joeycastillo/Sensor-Watch/PCB/Sensor Boards/Eagle (Legacy Boards)/Untested - WIP - Not Recommended/OSO-MISC-21-015 Temperature and Light Board.brd

## EAGLE design PCB/Sensor Boards/Eagle (Legacy Boards)/Untested - WIP - Not Recommended/OSO-MISC-21-015 Temperature and Light Board.brd (2021-10-25, an earlier design)

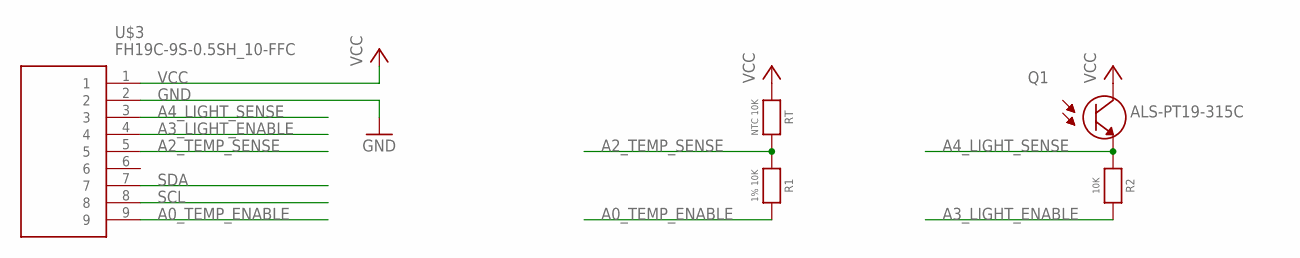
[picture p31: schematic OSO-MISC-21-015 Temperature and Light Board.sch]

Parts:
Q1: ALS-PT19-315C; XDCR_ALS-PT19-315C/L177/TR8_REVERSE
R1: 1% 10K; _0603MP
R2: 10K; _0603MP
RT: NTC 10K; _0603
U$3: FH19C-9S-0.5SH_10-FFC; FH19C9S05SH10-FFC

Connections:
A0_TEMP_ENABLE: R1.2, U$3.9
A2_TEMP_SENSE: R1.1, RT.2, U$3.5
A3_LIGHT_ENABLE: R2.2, U$3.4
A4_LIGHT_SENSE: Q1.2 (E), R2.1, U$3.3
GND: U$3.2
SCL: U$3.8
SDA: U$3.7
VCC: Q1.1 (C), RT.1, U$3.1

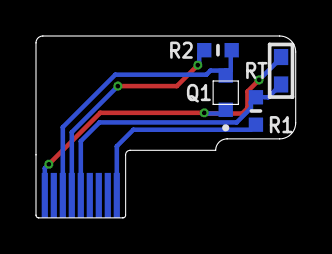
[picture p32: board OSO-MISC-21-015 Temperature and Light Board.brd from below]

Board: 2 copper layers, 14.4 x 10.1 mm, 5 parts (4 on the bottom side), 5 nets.
