joeycastillo/Sensor-Watch/PCB/Sensor Boards/Eagle (Legacy Boards)/Tested/OSO-MISC-21-021 Sensor Watch Motion II.brd

## EAGLE design PCB/Sensor Boards/Eagle (Legacy Boards)/Tested/OSO-MISC-21-021 Sensor Watch Motion II.brd (2022-02-05, an earlier design)

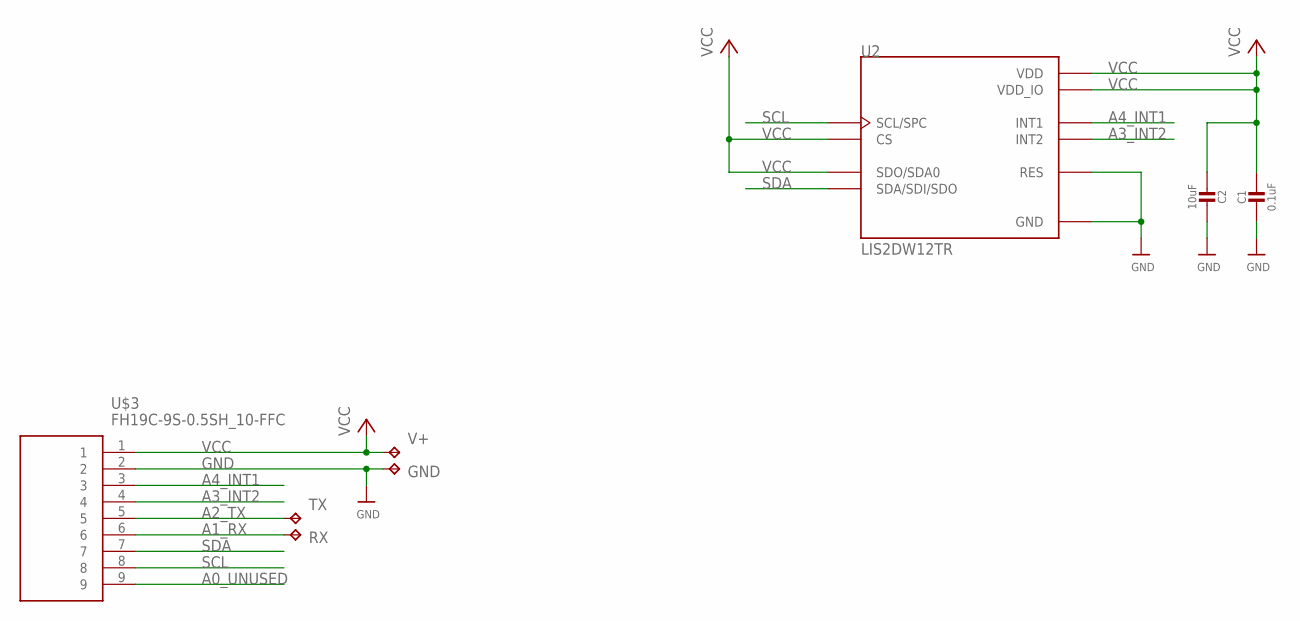
[picture p33: schematic OSO-MISC-21-021 Sensor Watch Motion II.sch]

Parts:
C1: 0.1uF; _0603MP
C2: 10uF; _0603MP
GND: TPB1,27; B1,27
RX: TPB1,27; B1,27
TX: TPB1,27; B1,27
U2: LIS2DW12TR; LGA12R50P4X4_200X200X70
U$3: FH19C-9S-0.5SH_10-FFC; FH19C9S05SH10-FFC
V+: TPB1,27; B1,27

Connections:
A0_UNUSED: U$3.9
A1_RX: RX.TP, U$3.6
A2_TX: TX.TP, U$3.5
A3_INT2: U2.11 (INT2), U$3.4
A4_INT1: U2.12 (INT1), U$3.3
GND: C1.2, C2.1, GND.TP, U2.6 (GND), U2.7 (RES), U2.8 (GND), U$3.2
SCL: U2.1 (SCL/SPC), U$3.8
SDA: U2.4 (SDA/SDI/SDO), U$3.7
VCC: C1.1, C2.2, U2.2 (CS), U2.3 (SDO/SDA0), U2.9 (VDD), U2.10 (VDD_IO), U$3.1, V+.TP

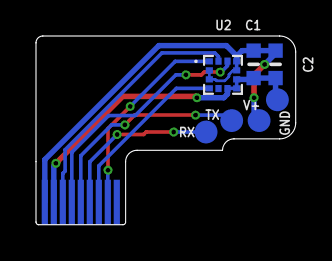
[picture p34: board OSO-MISC-21-021 Sensor Watch Motion II.brd from below]

Board: 2 copper layers, 14.4 x 10.5 mm, 8 parts (7 on the bottom side), 8 nets.
