joeycastillo/Sensor-Watch/PCB/Sensor Boards/BMI270-SensorBoard.brd

## EAGLE design PCB/Sensor Boards/Eagle (Legacy Boards)/Community/BMI270-SensorBoard.brd (2022-11-22, an earlier design)

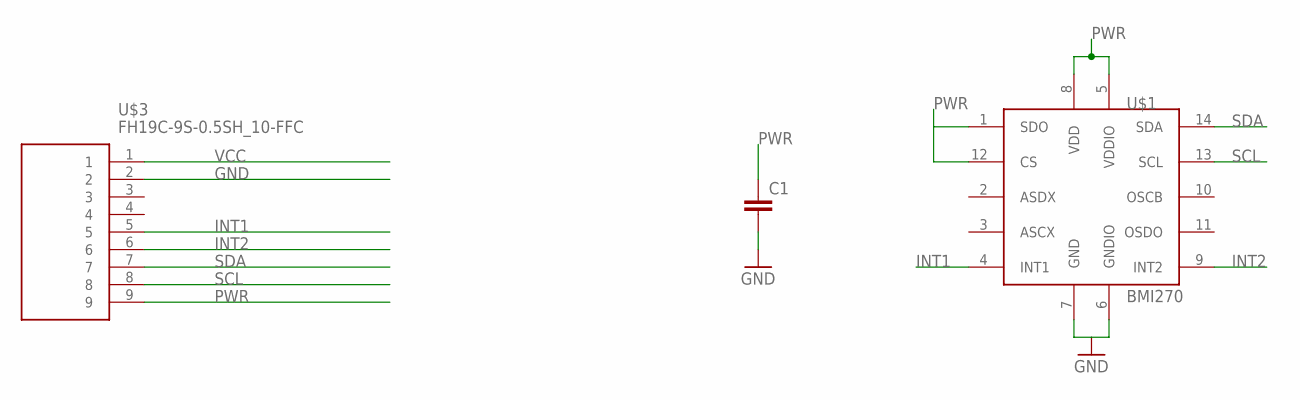
[picture p35: schematic BMI270-SensorBoard.sch]

Parts:
C1: C-EUC0603K; C0603K
U$1: BMI270; XDCR_BMI270
U$3: FH19C-9S-0.5SH_10-FFC; FH19C9S05SH10-FFC

Connections:
GND: C1.2, U$1.6 (GNDIO), U$1.7 (GND), U$3.2
INT1: U$1.4 (INT1), U$3.5
INT2: U$1.9 (INT2), U$3.6
PWR: C1.1, U$1.1 (SDO), U$1.5 (VDDIO), U$1.8 (VDD), U$1.12 (CS), U$3.9
SCL: U$1.13 (SCL), U$3.8
SDA: U$1.14 (SDA), U$3.7
VCC: U$3.1
