joeycastillo/Sensor-Watch/PCB/Sensor Boards/BMI270-SensorBoard.brd

## EAGLE design PCB/Sensor Boards/Eagle (Legacy Boards)/Community/BMI270-SensorBoard.brd (continued)

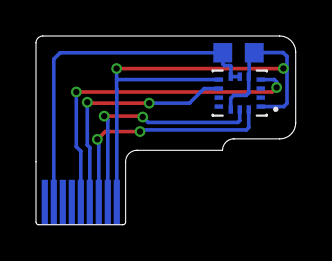
[picture p36: board BMI270-SensorBoard.brd from below]

Board: 2 copper layers, 14.4 x 10.5 mm, 3 parts (2 on the bottom side), 6 nets.
