joeycastillo/Sensor-Watch/PCB/Sensor Boards/Eagle (Legacy Boards)/Tested/OSO-MISC-21-019 Sensor Watch Test.brd

## EAGLE design PCB/Sensor Boards/Eagle (Legacy Boards)/Tested/OSO-MISC-21-019 Sensor Watch Test.brd (2021-11-22, an earlier design)

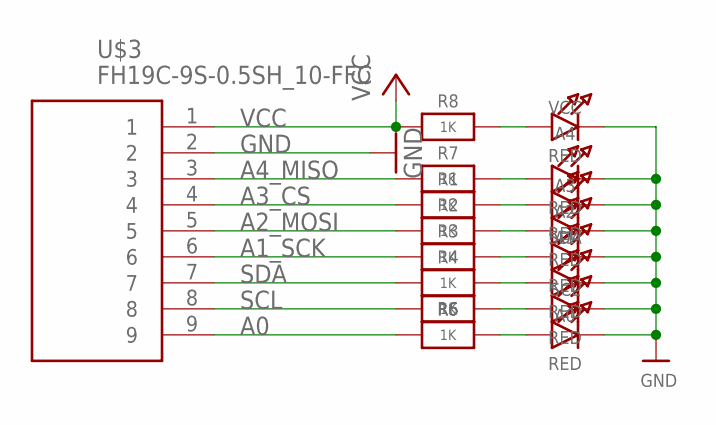
[picture p37: schematic OSO-MISC-21-019 Sensor Watch Test.sch]

Parts:
A0, A1, A2, A3, A4: RED; CHIPLED_0603_NOOUTLINE
R1, R2, R3, R4, R5, R6, R7, R8: 1K; _0603MP
SCL: RED; CHIPLED_0603_NOOUTLINE
SDA: RED; CHIPLED_0603_NOOUTLINE
U$3: FH19C-9S-0.5SH_10-FFC; FH19C9S05SH10-FFC
VCC: RED; CHIPLED_0603_NOOUTLINE

Connections:
A0: R6.1, U$3.9
A1_SCK: R3.1, U$3.6
A2_MOSI: R2.1, U$3.5
A3_CS: R1.1, U$3.4
A4_MISO: R7.1, U$3.3
GND: A0.C, A1.C, A2.C, A3.C, A4.C, SCL.C, SDA.C, U$3.2, VCC.C
unnamed: A4.A, R7.2
unnamed: A3.A, R1.2
unnamed: A2.A, R2.2
unnamed: A1.A, R3.2
unnamed: R4.2, SDA.A
unnamed: R5.2, SCL.A
unnamed: A0.A, R6.2
unnamed: R8.2, VCC.A
SCL: R5.1, U$3.8
SDA: R4.1, U$3.7
VCC: R8.1, U$3.1

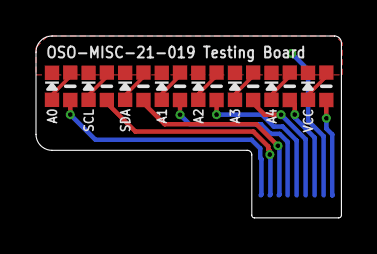
[picture p38: board OSO-MISC-21-019 Sensor Watch Test.brd from above]

Board: 2 copper layers, 17.0 x 10.1 mm, 17 parts (0 on the bottom side), 17 nets.
