joeycastillo/Sensor-Watch/PCB/Sensor Boards/Eagle (Legacy Boards)/Tested/OSO-MISC-21-002 Sensor Watch Environment.brd

## EAGLE design PCB/Sensor Boards/Eagle (Legacy Boards)/Tested/OSO-MISC-21-002 Sensor Watch Environment.brd (2021-04-10, an earlier design)

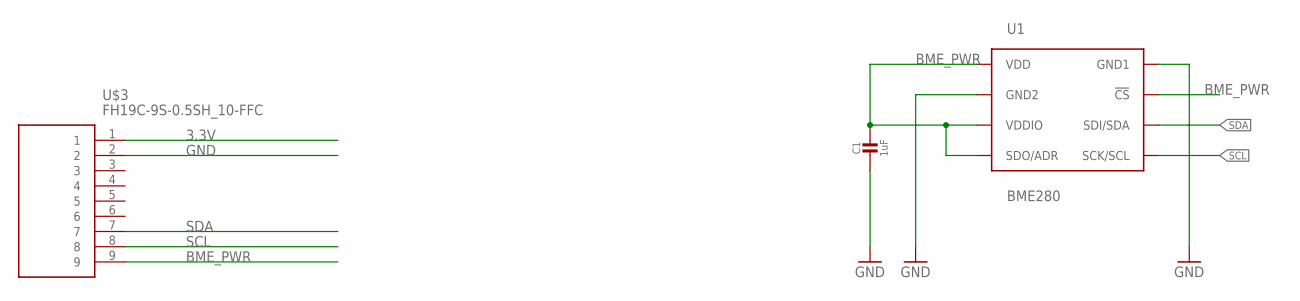
[picture p39: schematic OSO-MISC-21-002 Sensor Watch Environment.sch]

Parts:
C1: 1uF; _0603MP
U1: BME280; BME280_LGA
U$3: FH19C-9S-0.5SH_10-FFC; FH19C9S05SH10-FFC

Connections:
3.3V: U$3.1
BME_PWR: C1.1, U1.P$2 (!CS), U1.P$5 (SDO/ADR), U1.P$6 (VDDIO), U1.P$8 (VDD), U$3.9
GND: C1.2, U1.P$1 (GND1), U1.P$7 (GND2), U$3.2
SCL: U1.P$4 (SCK/SCL), U$3.8
SDA: U1.P$3 (SDI/SDA), U$3.7

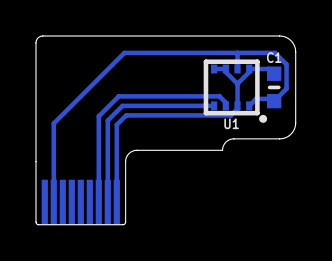
[picture p40: board OSO-MISC-21-002 Sensor Watch Environment.brd from below]

Board: 2 copper layers, 14.4 x 10.5 mm, 3 parts (2 on the bottom side), 4 nets.
