joeycastillo/Sensor-Watch/watch-library/hardware/hw/driver_init.h

/*
 * Code generated from Atmel Start.
 *
 * This file will be overwritten when reconfiguring your Atmel Start project.
 * Please copy examples or other code you want to keep to a separate file
 * to avoid losing it when reconfiguring.
 */
#ifndef DRIVER_INIT_INCLUDED
#define DRIVER_INIT_INCLUDED

#define GPIO_PIN_FUNCTION_A 0
#define GPIO_PIN_FUNCTION_B 1
#define GPIO_PIN_FUNCTION_C 2
#define GPIO_PIN_FUNCTION_D 3
#define GPIO_PIN_FUNCTION_E 4
#define GPIO_PIN_FUNCTION_F 5
#define GPIO_PIN_FUNCTION_G 6
#define GPIO_PIN_FUNCTION_H 7
#define GPIO_PIN_FUNCTION_I 8

#include "pins.h"

#ifdef __cplusplus
extern "C" {
#endif

#include <hal_atomic.h>
#include <hal_delay.h>
#include <hal_gpio.h>
#include <hal_init.h>
#include <hal_io.h>
#include <hal_sleep.h>
#include <hal_ext_irq.h>
#include <hal_i2c_m_sync.h>
#include <hal_spi_m_sync.h>
#include <hal_usart_sync.h>
#include <hal_delay.h>
#include <hal_slcd_sync.h>

extern struct adc_sync_descriptor ADC_0;

extern struct i2c_m_sync_desc I2C_0;

extern struct usart_sync_descriptor USART_0;

extern struct spi_m_sync_descriptor SPI_0;

extern struct slcd_sync_descriptor SEGMENT_LCD_0;

void I2C_0_CLOCK_init(void);
void I2C_0_init(void);
void I2C_0_PORT_init(void);

void SPI_0_PORT_init(void);
void SPI_0_CLOCK_init(void);
void SPI_0_init(void);

void delay_driver_init(void);

void EXTERNAL_IRQ_0_init(void);

void SEGMENT_LCD_0_PORT_init(void);
void SEGMENT_LCD_0_init(void);

#ifdef __cplusplus
}
#endif
#endif // DRIVER_INIT_INCLUDED
